brunohorta82/BH_OnOfre/CAIXAS_CASES/Onofre Livolo/img1.png

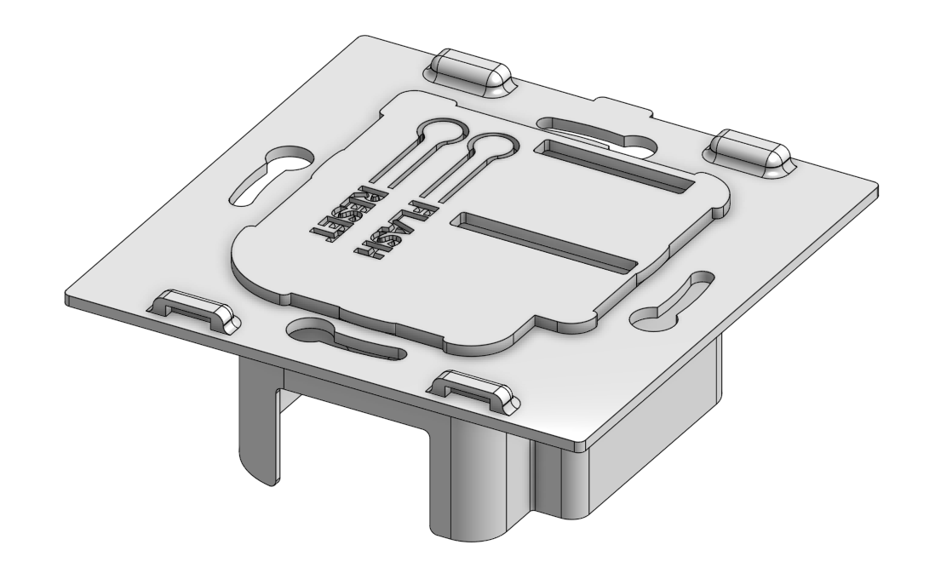
CAIXAS_CASES/Onofre Livolo/img1.png
