brunohorta82/BH_OnOfre/CAIXAS_CASES/Onofre Livolo/img2.png

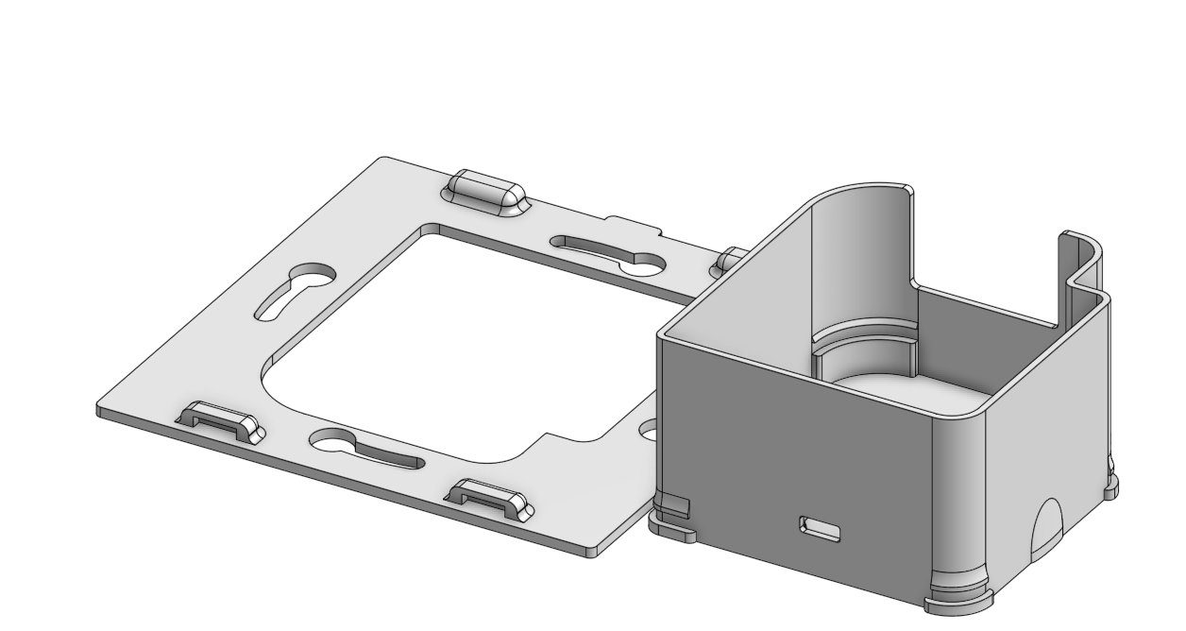
CAIXAS_CASES/Onofre Livolo/img2.png
