brunohorta82/BH_OnOfre/CAIXAS_CASES/Onofre Prot/img1.png

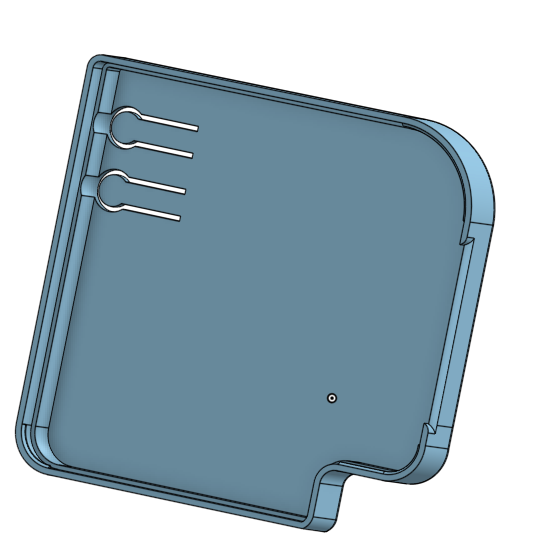
CAIXAS_CASES/Onofre Prot/img1.png
