brunohorta82/BH_OnOfre/CAIXAS_CASES/Onofre Prot/img2.png

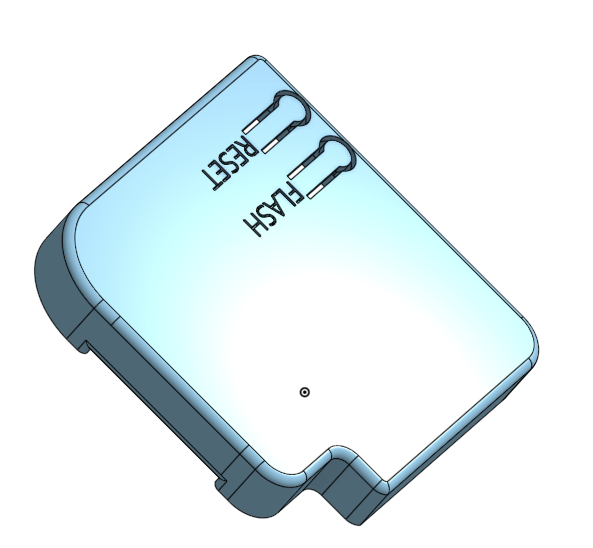
CAIXAS_CASES/Onofre Prot/img2.png
